ArtiomSu/ManaBall-Trackball/finished stl/buttons/simple single button test.stl

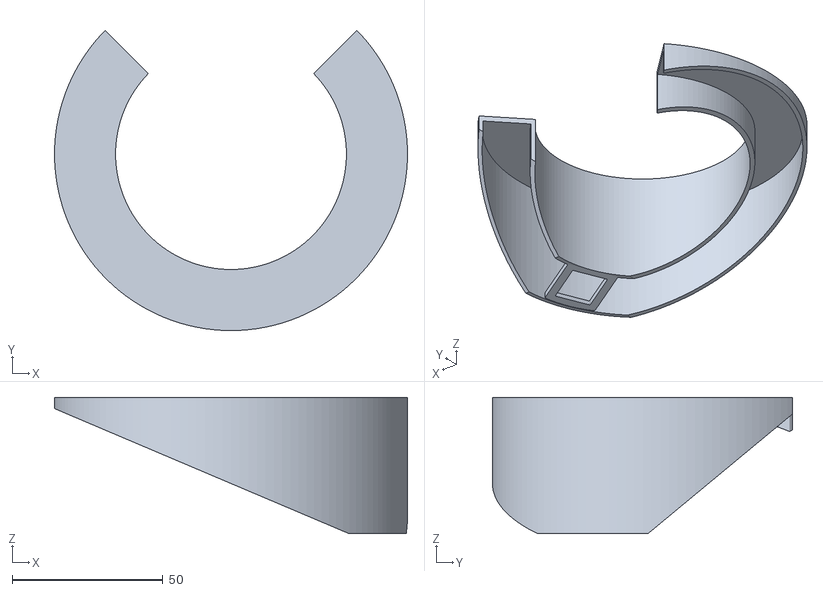
[picture p34: CAD file, 2025-11-09]
finished stl/buttons/simple single button test.stl
117.0 x 99.5 x 45.2
