ArtiomSu/ManaBall-Trackball/finished stl/buttons/simple single button test flipped.stl

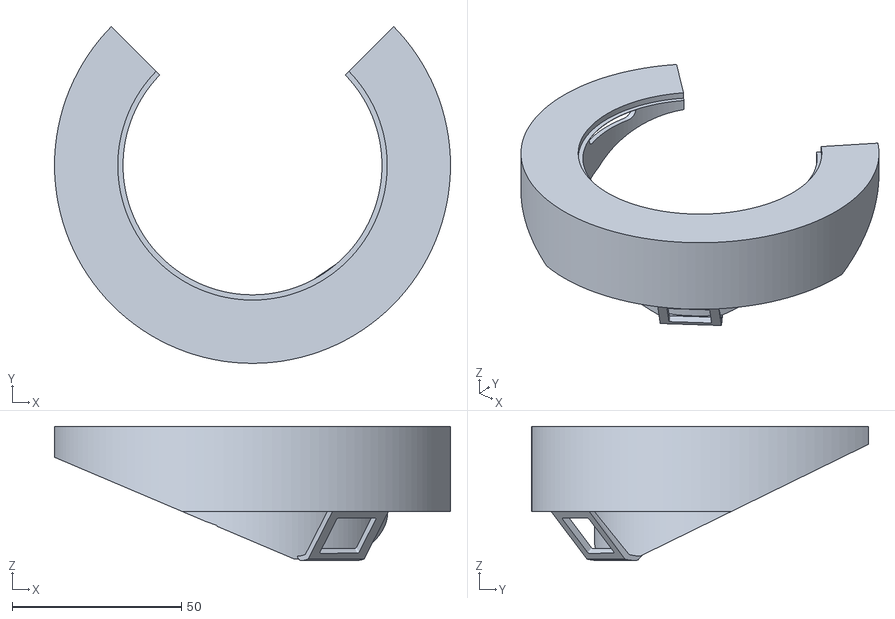
[picture p35: CAD file, 2025-11-09]
finished stl/buttons/simple single button test flipped.stl
117.0 x 99.5 x 39.7
