ArtiomSu/ManaBall-Trackball/finished stl/buttons/simple triple button test.stl

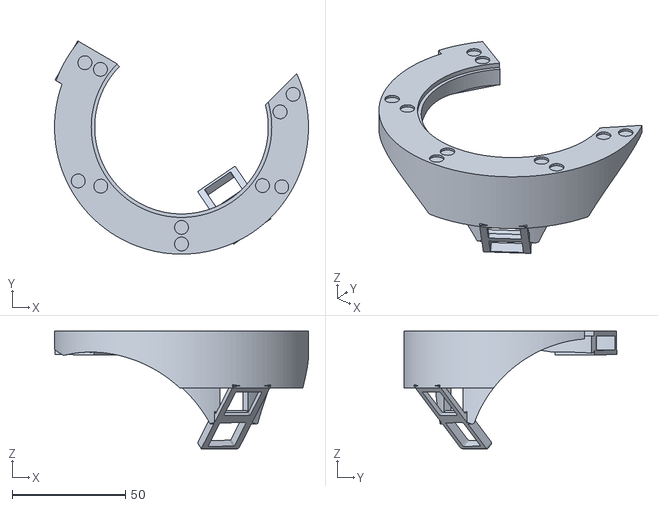
[picture p36: CAD file, 2025-11-09]
finished stl/buttons/simple triple button test.stl
112.0 x 94.1 x 51.8
